kostas-dot/arduino_car_v4.5.6/2473098_cn6000/images/arduino-uno-r4-wifi.jpg

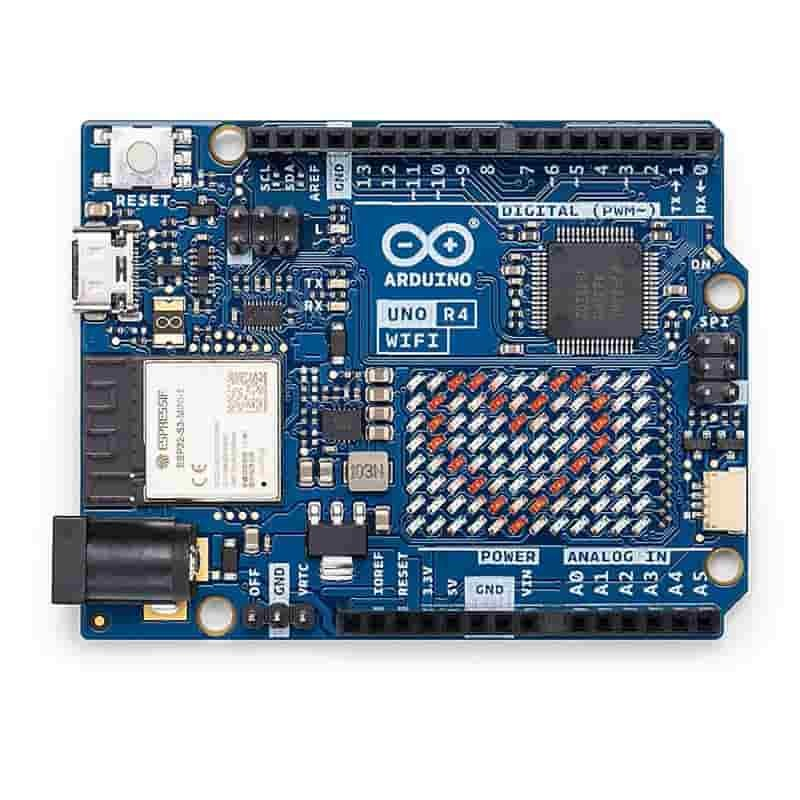
2473098_cn6000/images/arduino-uno-r4-wifi.jpg
