kostas-dot/arduino_car_v4.5.6/2473098_cn6000/images/Arduino_Done_Uploading_Linux.png

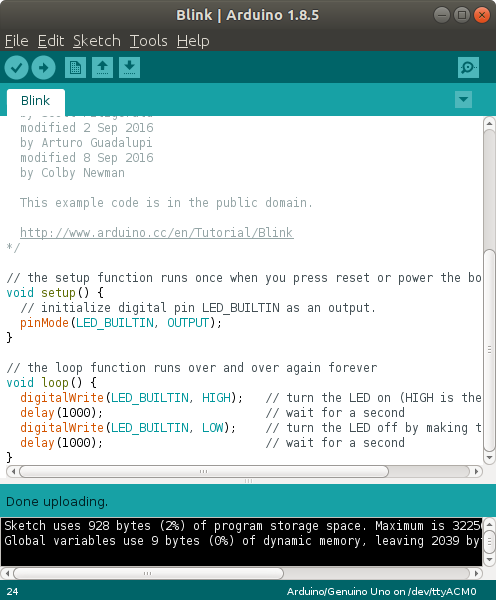
2473098_cn6000/images/Arduino_Done_Uploading_Linux.png
