kostas-dot/arduino_car_v4.5.6/2473098_cn6000/images/broker-main-controller.jpg

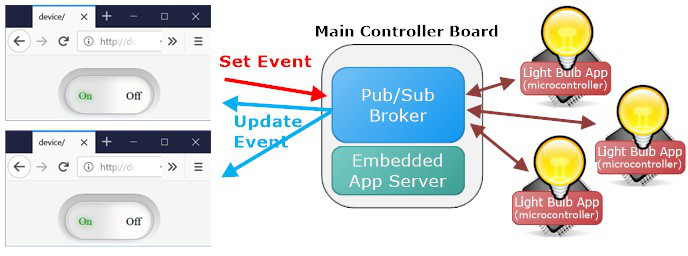
2473098_cn6000/images/broker-main-controller.jpg
