kostas-dot/arduino_car_v4.5.6/2473098_cn6000/images/correlationphotoelectricinfraredcountslotsensormodule10mm-2048x2048-500x5002.png

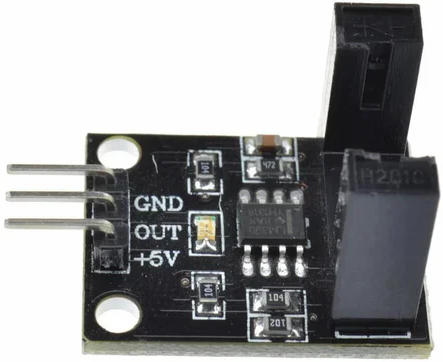
2473098_cn6000/images/correlationphotoelectricinfraredcountslotsensormodule10mm-2048x2048-500x5002.png
