kostas-dot/arduino_car_v4.5.6/2473098_cn6000/images/IMG_0022.PNG

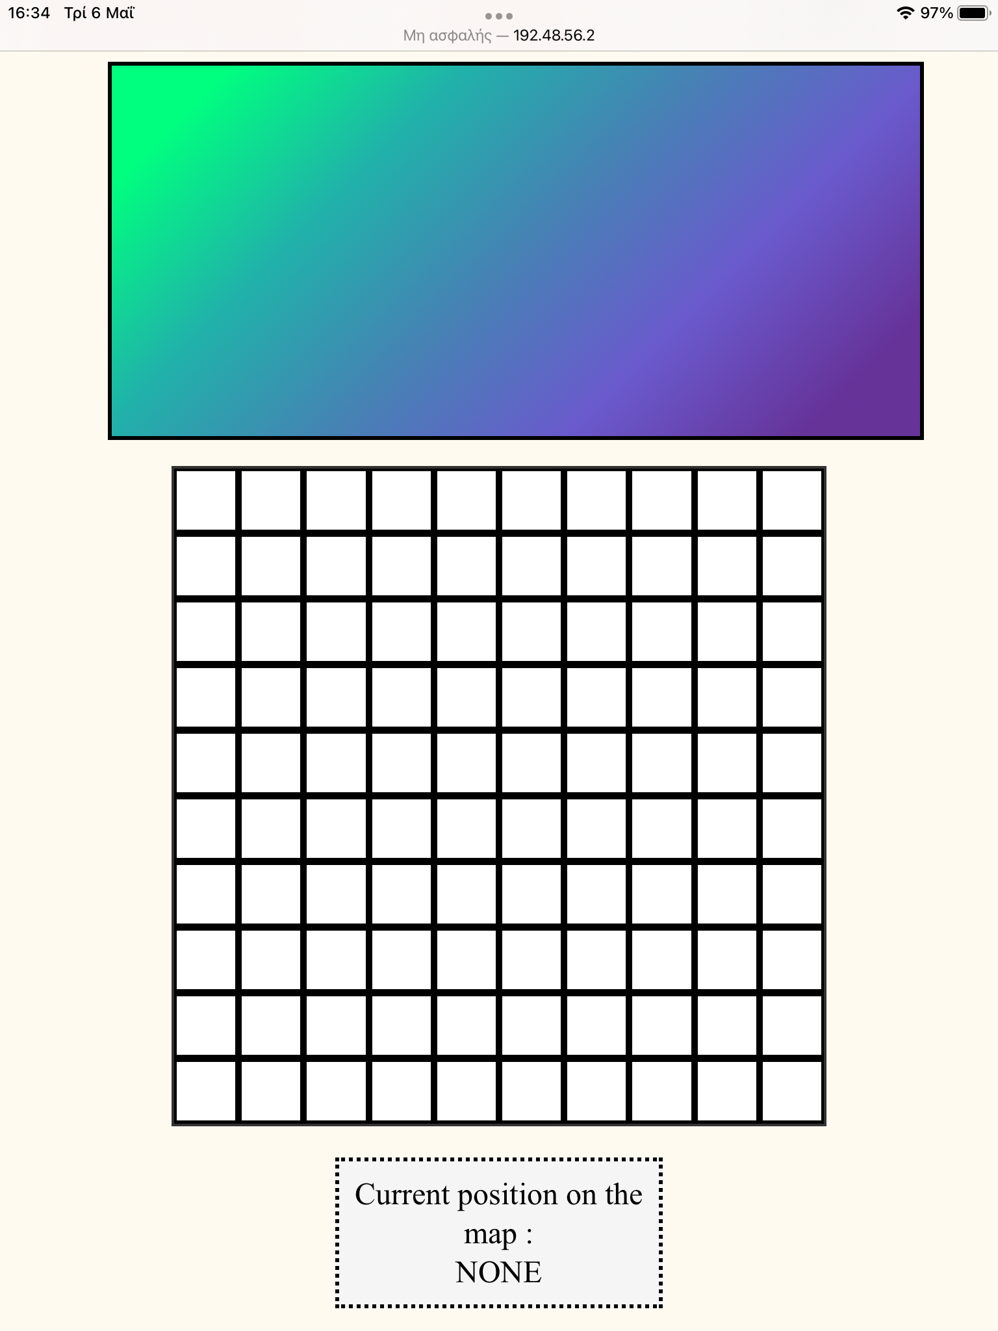
2473098_cn6000/images/IMG_0022.PNG
