kostas-dot/arduino_car_v4.5.6/2473098_cn6000/images/sonic_bb.png

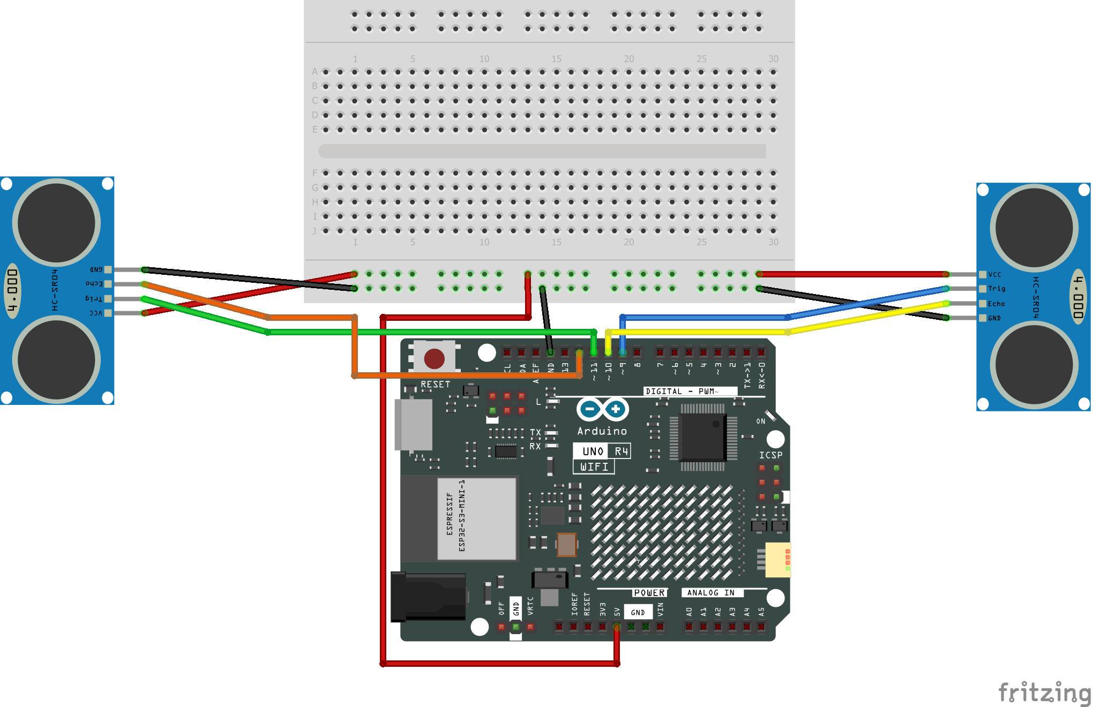
2473098_cn6000/images/sonic_bb.png
